jmA500/Key-Tap/src/attiny-rgb/key_tap.h

/************************************************************************
Title:    Amiga Keyboard listener and decoder functions

Author:   Jan Metzger <jm@metweb.de>

License:  GNU General Public License 

LICENSE:
    Copyright (C) 2014 Jan Metzger

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
************************************************************************/

#ifndef KEY_TAP_H
#define KEY_TAP_H

#include <stdint.h>
#include <avr/io.h>

/* These variables configure the timer for timeout. 
   The timer should trigger every 40 us, and 
   TIMELEFT_INIT gives the numer of timer cycles per 
   bit before reading a byte from the keyboard 
   is canceled */
#define TIMER0_OCR          25
#define TIMELEFT_INIT       7

/* cycles of 40 us */
#define TIME_RESET          256-20

/* cycles of 10 ms */
#define TIME_RES_COUNT_LONG    400

/* Configure the Pins here */
#define KBD_DATA_PIN  PINA
#define KBD_DATA_BIT  PA0 

#define KBD_RESET_PIN  PINA
#define KBD_RESET_PORT PORTA
#define KBD_RESET_DDR  DDRA
#define KBD_RESET_BIT PA1 

/* Keycodes */
#define KEY_F1     0x50
#define KEY_F2     0x51
#define KEY_F3     0x52
#define KEY_F4     0x53
#define KEY_F5     0x54
#define KEY_F6     0x55
#define KEY_F7     0x56
#define KEY_F8     0x57
#define KEY_F9     0x58
#define KEY_F10    0x59
#define KEY_HELP   0x5f
#define KEY_SHIFTL 0x60 
#define KEY_SHIFTR 0x61
#define KEY_DELETE 0x46

#define KBD_FLAG_KEY_AVAILABLE  0x01
#define KBD_FLAG_GOT_RESET      0x02
#define KBD_FLAG_GOT_LONG_RESET 0x04

typedef struct 
{
  uint8_t data;
  uint8_t flags;
} kbd_ctl_t;

extern volatile kbd_ctl_t kbd_ctl;

/* Initialize keyboard functions. */
void kbd_init();

/* Returns 1 if a key press is detected, then the argument holds the keycode.
   Returns 0 otherwise and leaves argument unchanged. */
uint8_t kbd_get_key(uint8_t* res);

/* Check flags for reset */
uint8_t kbd_got_reset();

/* Check flags for long reset */
uint8_t kbd_got_long_reset();

/* Reset the Amiga via Kbd_reset */
void    kbd_do_reset();
 
#endif
