jmA500/Key-Tap/src/attiny-rgb/uart4313.c

/************************************************************************
Title:    Interrupt UART library with receive/transmit circular buffers

Original Author:   Peter Fleury <pfleury@gmx.ch>
Modified by:       Jan Metzger <jm@metweb.de>

License:  GNU General Public License 

LICENSE:
    Copyright (C) 2006 Peter Fleury
    Copyright (C) 2014 Jan Metzger

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
************************************************************************/

#include "uart.h"

#include <avr/io.h>
#include <avr/interrupt.h>
#include <avr/sleep.h>

#define UART_UBRR       ((F_CPU+UART_BAUD_RATE*8)/(UART_BAUD_RATE*16)-1)
#define UART_BAUD_REAL  (F_CPU/(16*(UART_UBRR+1)))
#define UART_BAUD_ERROR ((UART_BAUD_REAL*1000)/UART_BAUD_RATE) 
 
#if ((UART_BAUD_ERROR<990) || (UART_BAUD_ERROR>1010))
  #error Baud Rate error too high
#endif

volatile uart_rx_buffer_t uart_rx_buffer;
volatile uart_tx_buffer_t uart_tx_buffer;
volatile uint8_t uart_tx_free;

/**
 * declaration of functions
 */
uint8_t uart_tx_buffer_full();

void uart_init()
{
  // enable RX, TX, RX interrupt
  UCSRB |= (1<<TXEN) | (1 << RXEN) | (1 << RXCIE);
  
  // 8 data bits
  UCSRC |= (1 << UCSZ1) | (1 << UCSZ0);
  
  // set baudrate
  UBRRH = UART_UBRR >> 8;
  UBRRL = UART_UBRR & 0xFF;

  uart_tx_free =1;
  uart_rx_buffer.writepos = 0;
  uart_rx_buffer.readpos  = 0;
  uart_tx_buffer.writepos = 0;
  uart_tx_buffer.readpos  = 0;
}

void uart_clear_rx_buffer()
{
  uint8_t sreg_save = SREG;
  cli();      
  
  uart_rx_buffer.readpos = 0;
  uart_rx_buffer.writepos = 0;

  SREG = sreg_save;
}

void uart_putc_int(char c)
{
  uint8_t sreg_save = SREG;
  cli();

  if (UCSRA & (1<<UDRE))
    // transmitter free, transmit
    {
      UDR = c;
      uart_tx_free = 0;
    }
  else
    // transmitter busy, write to buffer, enable interrupt
    {
      uint8_t tmp = uart_tx_buffer.writepos;
      uart_tx_buffer.buffer[tmp] = c;
      tmp++;
      tmp &= (UART_TX_BUFSIZE-1);
      uart_tx_buffer.writepos = tmp;
    }
  UCSRB |= (1 << UDRIE);
  SREG = sreg_save;
}

void uart_putc(char c)
{
  while (uart_tx_buffer_full())
    {
      set_sleep_mode(SLEEP_MODE_IDLE);
      sleep_mode();
    }
  uart_putc_int(c);
}

void uart_puts (const char *s)
{
  while (*s)
    {
      uart_putc(*s);
      s++;
    }
}

void uart_puts_p (const char * PROGMEM s)
{
  char c;
  while ( (c = pgm_read_byte(s)) )
    {
      uart_putc(c);
      s++;
    }
}

uint8_t uart_tx_buffer_bytes()
{
  if (uart_tx_buffer.writepos < uart_tx_buffer.readpos)
    return (uart_tx_buffer.readpos - uart_tx_buffer.writepos);
  else 
    return (uart_tx_buffer.writepos - uart_tx_buffer.readpos);
}

uint8_t uart_rx_buffer_bytes()
{
  if (uart_rx_buffer.writepos < uart_rx_buffer.readpos)
    return (uart_rx_buffer.readpos - uart_rx_buffer.writepos);
  else 
    return (uart_rx_buffer.writepos - uart_rx_buffer.readpos);
}

uint8_t uart_tx_char_present()
{
  return (uart_tx_buffer.writepos != uart_tx_buffer.readpos);
}

uint8_t uart_rx_char_present()
{
  return (uart_rx_buffer.writepos != uart_rx_buffer.readpos);
}

void uart_tx_wait()
{
  while (uart_tx_free==0)
    {
      set_sleep_mode(SLEEP_MODE_IDLE);
      sleep_mode();
    }
}

uint8_t uart_tx_buffer_full()
{
  uint8_t sreg_save = SREG;
  cli();

  uint8_t res = 0;
  uint8_t tmp = uart_tx_buffer.writepos;
  tmp++;
  tmp &= (UART_TX_BUFSIZE-1);

  if (uart_tx_buffer.readpos == tmp)
    res = 1;
  
  SREG = sreg_save;
  return res;
}

char uart_getc()
{
  uint8_t tmp = uart_rx_buffer.readpos;

  while (uart_rx_buffer.writepos == tmp)
    { }

  uint8_t sreg_save = SREG;
  cli();
  
  char res = uart_rx_buffer.buffer[tmp];  
  tmp++;
  tmp &= (UART_RX_BUFSIZE-1);
  uart_rx_buffer.readpos = tmp;
  SREG = sreg_save;

  return res;
}

ISR(USART_UDRE_vect)
{
  uint8_t tmp = uart_tx_buffer.readpos;
  if (uart_tx_buffer.writepos != tmp)
    // data in buffer
    {
      UDR = uart_tx_buffer.buffer[tmp];
      tmp++;
      tmp &= (UART_TX_BUFSIZE-1);
      uart_tx_buffer.readpos = tmp;
    }
  else
    // no data, so disable interrupt
    {
      UCSRB &= ~(1 << UDRIE);
      uart_tx_free = 1;
    }
}

ISR(USART_RX_vect) 
{
  uint8_t tmp = uart_rx_buffer.writepos;
  uart_rx_buffer.buffer[tmp] = UDR;
  tmp++;
  tmp &= (UART_RX_BUFSIZE - 1);  
  uart_rx_buffer.writepos = tmp;
}
